Squalius-cephalus/suutari20/vial_firmware/suutari20/keymaps/vial/config.h

/* SPDX-License-Identifier: GPL-2.0-or-later */

#pragma once

#define DYNAMIC_KEYMAP_LAYER_COUNT 8
#define VIAL_KEYBOARD_UID {0x39, 0x6B, 0x9C, 0x86, 0x5B, 0x1E, 0x93, 0xB7}
#define VIAL_UNLOCK_COMBO_ROWS { 1, 2 }
#define VIAL_UNLOCK_COMBO_COLS { 5, 5 }
